ezzcodeezzlife/LED-Cube/Final/led-cube-sketch/data/textures/nx.png

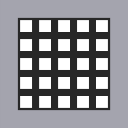
Final/led-cube-sketch/data/textures/nx.png
